Canorus/mapadubu/documents/images/IMG_3020.JPG

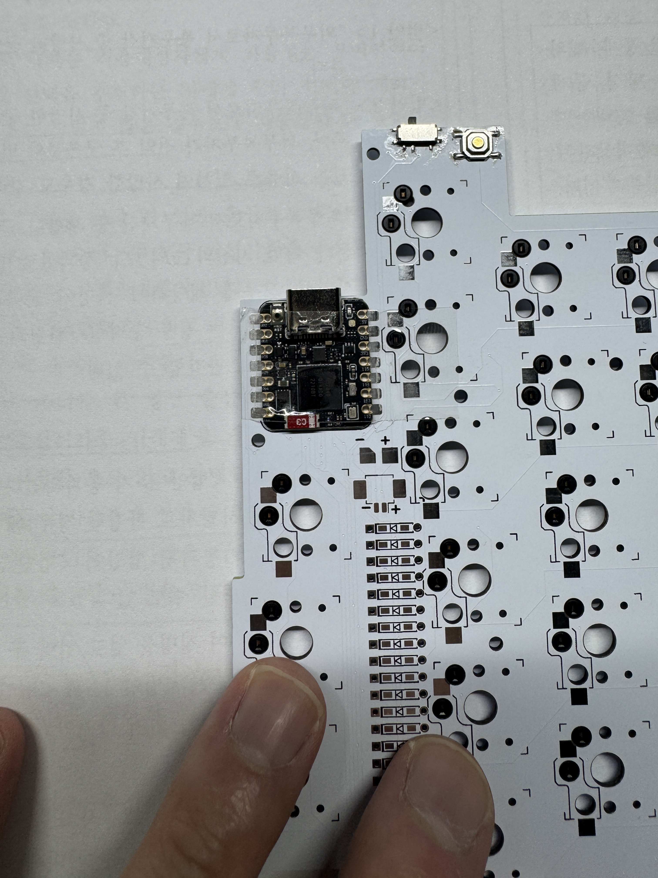
documents/images/IMG_3020.JPG
