Canorus/mapadubu/documents/images/IMG_3026.JPG

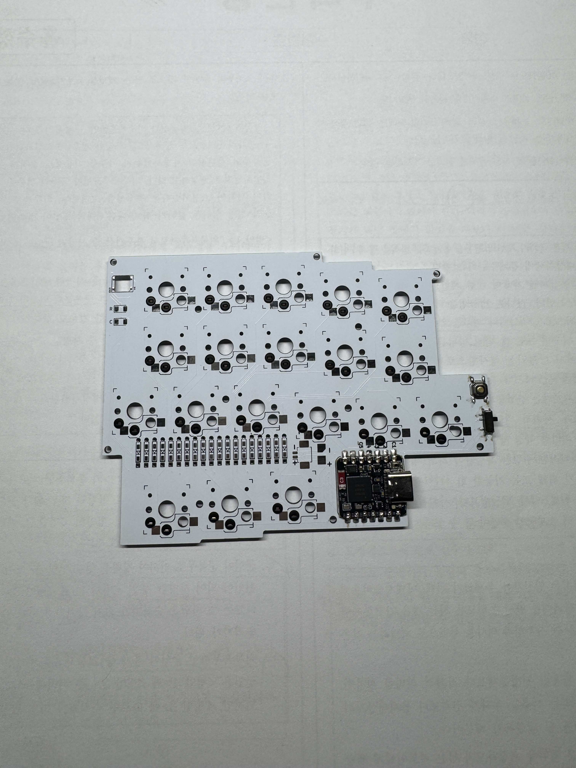
documents/images/IMG_3026.JPG
