Canorus/mapadubu/documents/images/IMG_3027.JPG

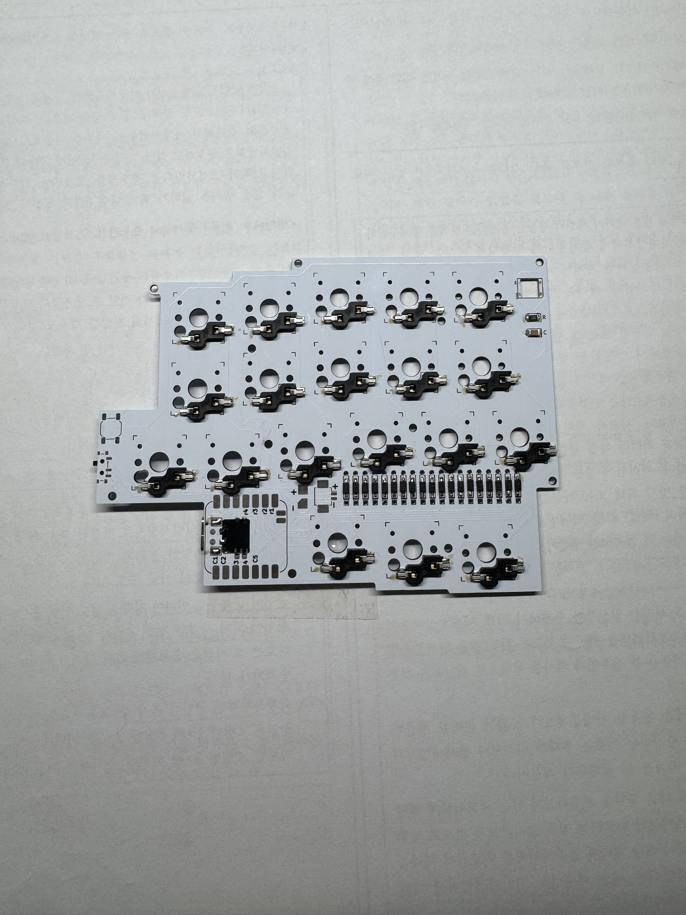
documents/images/IMG_3027.JPG
