Canorus/mapadubu/documents/images/IMG_3028.JPG

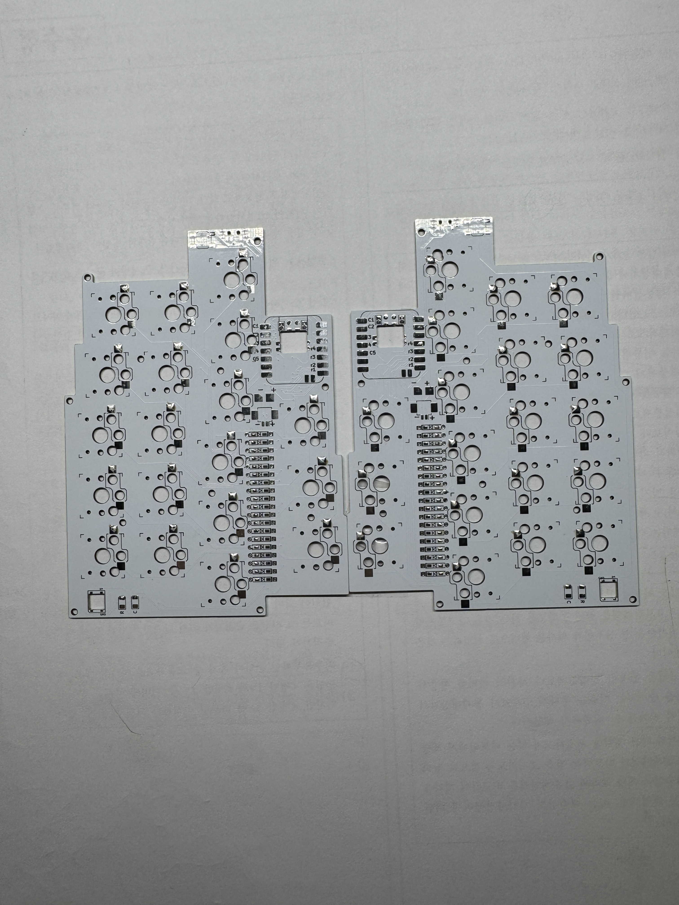
documents/images/IMG_3028.JPG
