Canorus/mapadubu/kicad/mapadubu_19.05mm.kicad_sch

## KiCad design kicad/mapadubu_19.05mm.kicad_sch (2026-05-23)

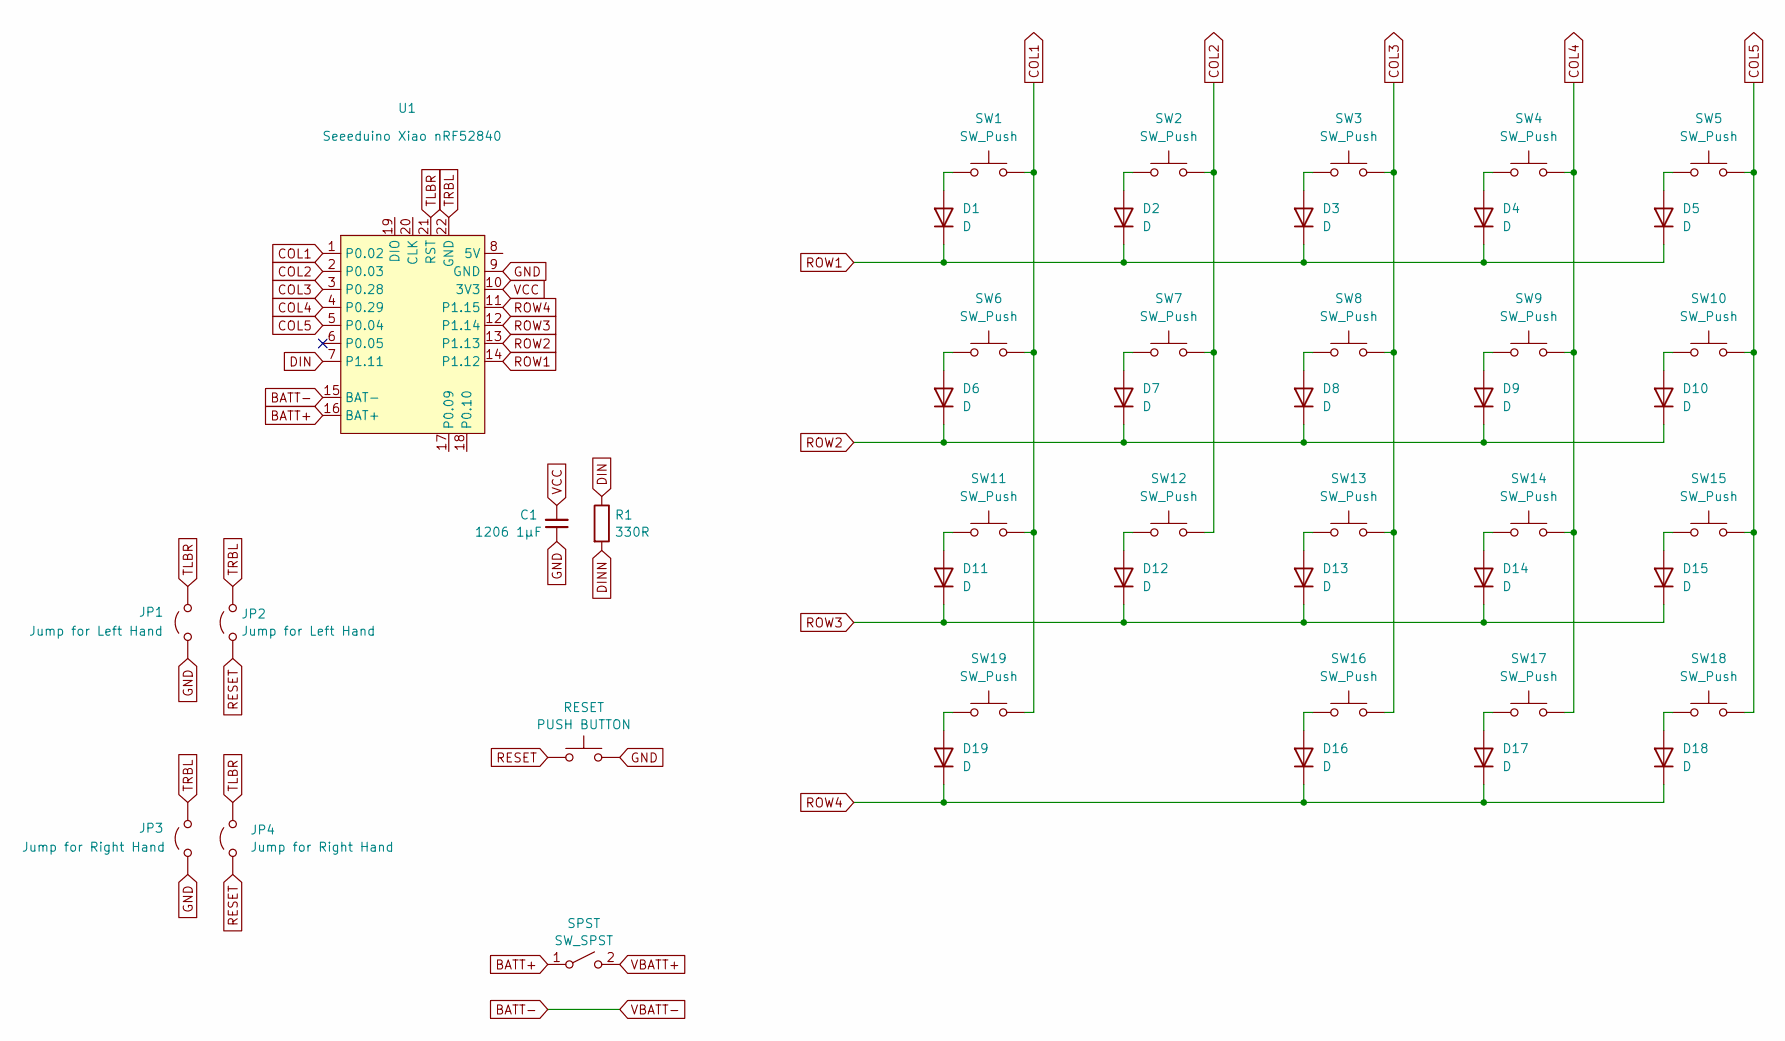
[picture p16: schematic mapadubu_19.05mm.kicad_sch]

Parts:
C1: 1206 1µF
D1, D2, D3, D4, D5, D6, D7, D8, D9, D10, D11, D12, D13, D14, D15, D16, D17, D18, D19: D
JP1, JP2: Jump for Left Hand
JP3, JP4: Jump for Right Hand
R1: 330R
RESET: PUSH BUTTON
SPST: SW_SPST
SW1, SW2, SW3, SW4, SW5, SW6, SW7, SW8, SW9, SW10, SW11, SW12, SW13, SW14, SW15, SW16, SW17, SW18, SW19: SW_Push
U1: Seeeduino Xiao nRF52840; Xiao_nRF52840_ACH

Connections:
BATT+: SPST.1 (A), U1.16 (BAT+)
BATT-: U1.15 (BAT-)
COL1: SW1.2, SW6.2, SW11.2, SW19.2, U1.1 (P0.02)
COL2: SW2.2, SW7.2, SW12.2, U1.2 (P0.03)
COL3: SW3.2, SW8.2, SW13.2, SW16.2, U1.3 (P0.28)
COL4: SW4.2, SW9.2, SW14.2, SW17.2, U1.4 (P0.29)
COL5: SW5.2, SW10.2, SW15.2, SW18.2, U1.5 (P0.04)
DIN: R1.1, U1.7 (P1.11)
DINN: R1.2
GND: C1.1, JP1.1 (A), JP3.1 (A), RESET.2, U1.9 (GND)
unnamed: D1.2 (A), SW1.1
unnamed: D2.2 (A), SW2.1
unnamed: D3.2 (A), SW3.1
unnamed: D4.2 (A), SW4.1
unnamed: D5.2 (A), SW5.1
unnamed: D6.2 (A), SW6.1
unnamed: D7.2 (A), SW7.1
unnamed: D8.2 (A), SW8.1
unnamed: D9.2 (A), SW9.1
unnamed: D10.2 (A), SW10.1
unnamed: D11.2 (A), SW11.1
unnamed: D12.2 (A), SW12.1
unnamed: D13.2 (A), SW13.1
unnamed: D14.2 (A), SW14.1
unnamed: D15.2 (A), SW15.1
unnamed: D16.2 (A), SW16.1
unnamed: D17.2 (A), SW17.1
unnamed: D18.2 (A), SW18.1
unnamed: D19.2 (A), SW19.1
RESET: JP2.1 (A), JP4.1 (A), RESET.1
ROW1: D1.1 (K), D2.1 (K), D3.1 (K), D4.1 (K), D5.1 (K), U1.14 (P1.12)
ROW2: D6.1 (K), D7.1 (K), D8.1 (K), D9.1 (K), D10.1 (K), U1.13 (P1.13)
ROW3: D11.1 (K), D12.1 (K), D13.1 (K), D14.1 (K), D15.1 (K), U1.12 (P1.14)
ROW4: D16.1 (K), D17.1 (K), D18.1 (K), D19.1 (K), U1.11 (P1.15)
TLBR: JP1.2 (B), JP4.2 (B), U1.21 (RST)
TRBL: JP2.2 (B), JP3.2 (B), U1.22 (GND)
VBATT+: SPST.2 (B)
VCC: C1.2, U1.10 (3V3)
